maxiro-samurai/M-heat/Image/1.bmp

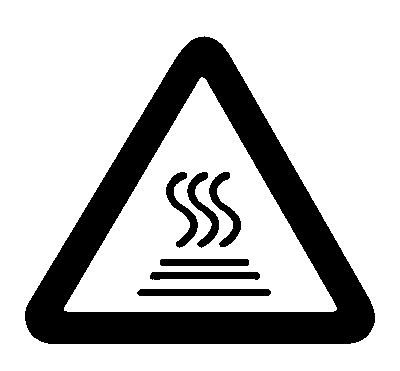
Image/1.bmp
