maxiro-samurai/M-heat/Image/e9a1dba946c36db57aece537687ce84.jpg

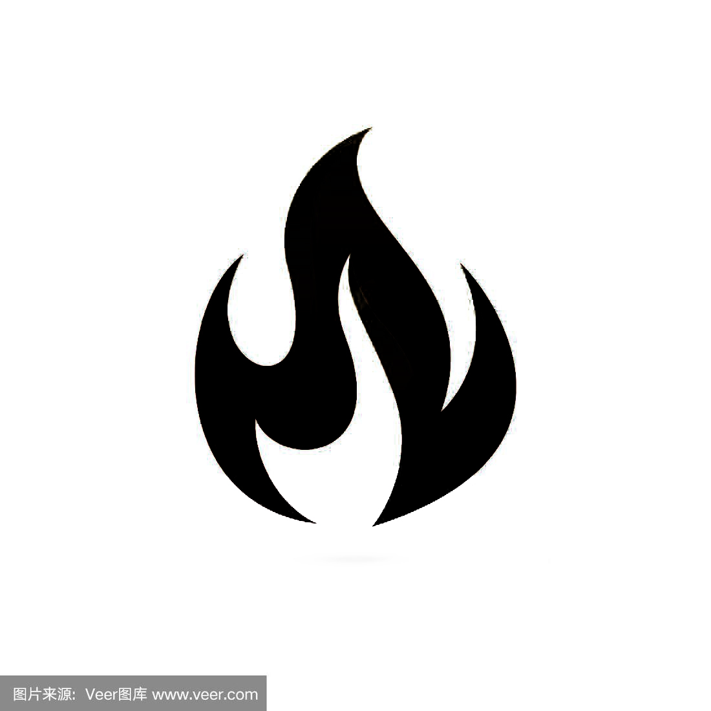
Image/e9a1dba946c36db57aece537687ce84.jpg
