maxiro-samurai/M-heat/Image/fire.bmp

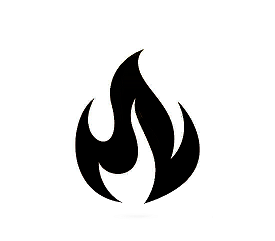
Image/fire.bmp
