maxiro-samurai/M-heat/Image/IMG_1925.JPG

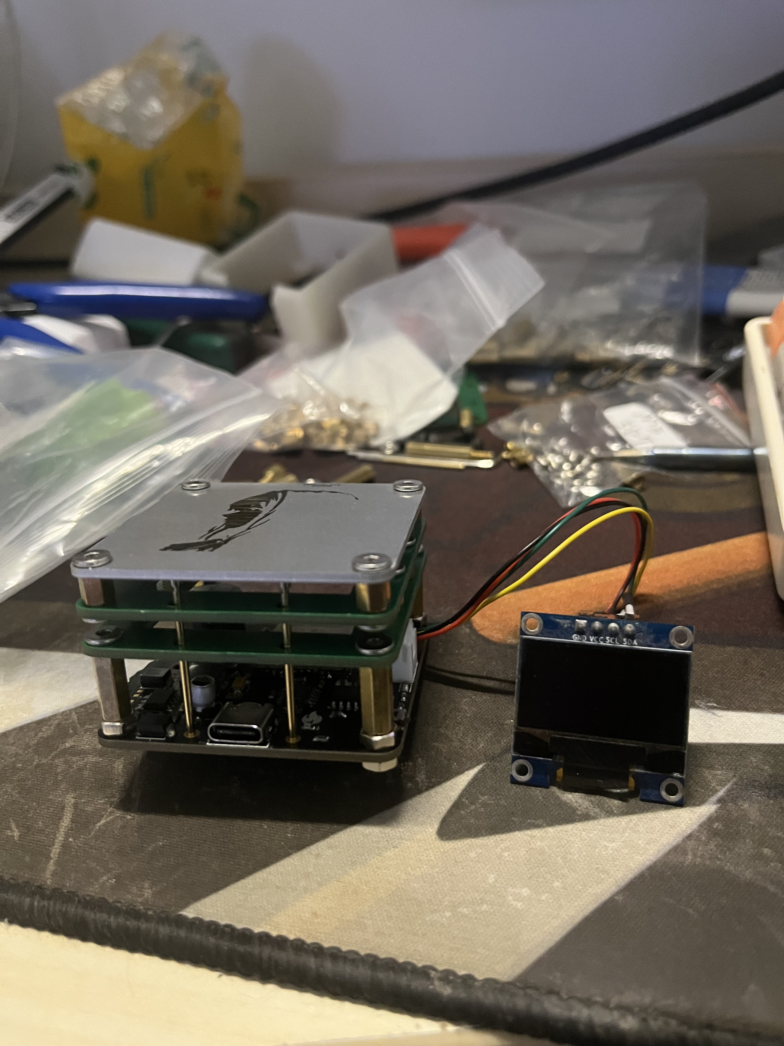
Image/IMG_1925.JPG
