maxiro-samurai/M-heat/Image/IMG_1926.JPG

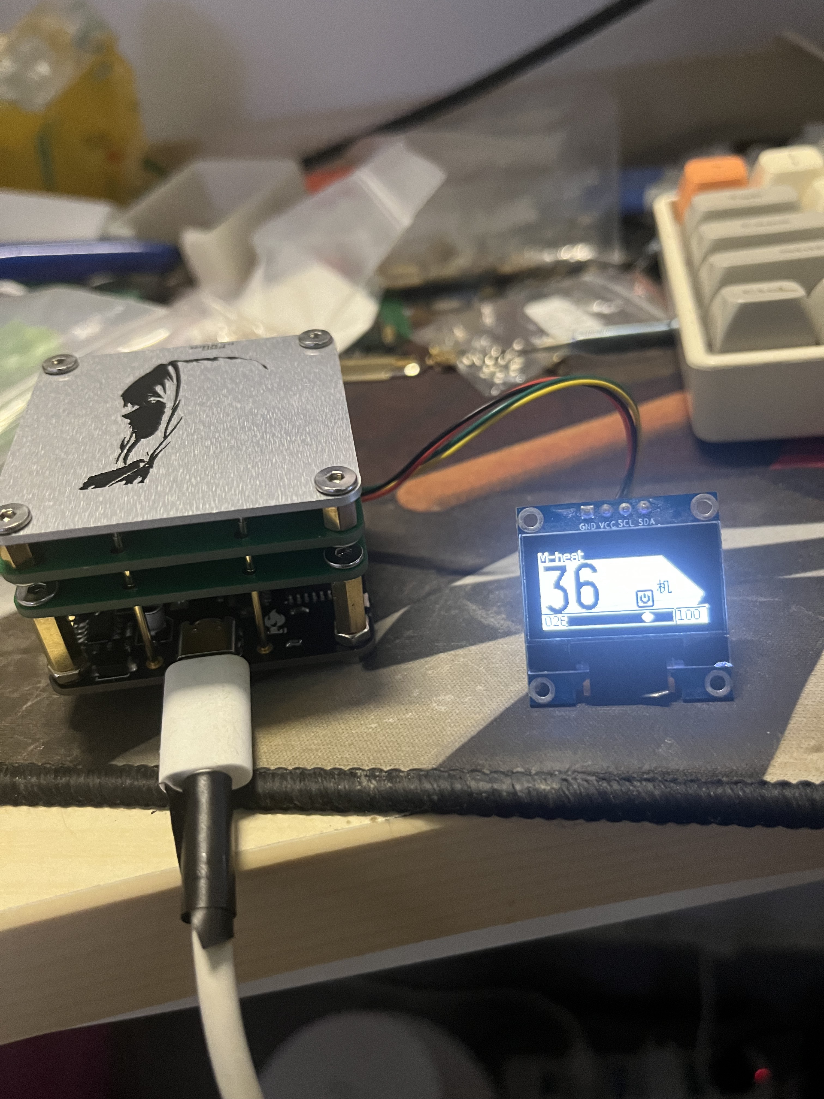
Image/IMG_1926.JPG
