maxiro-samurai/M-heat/Image/IMG_1927.JPG

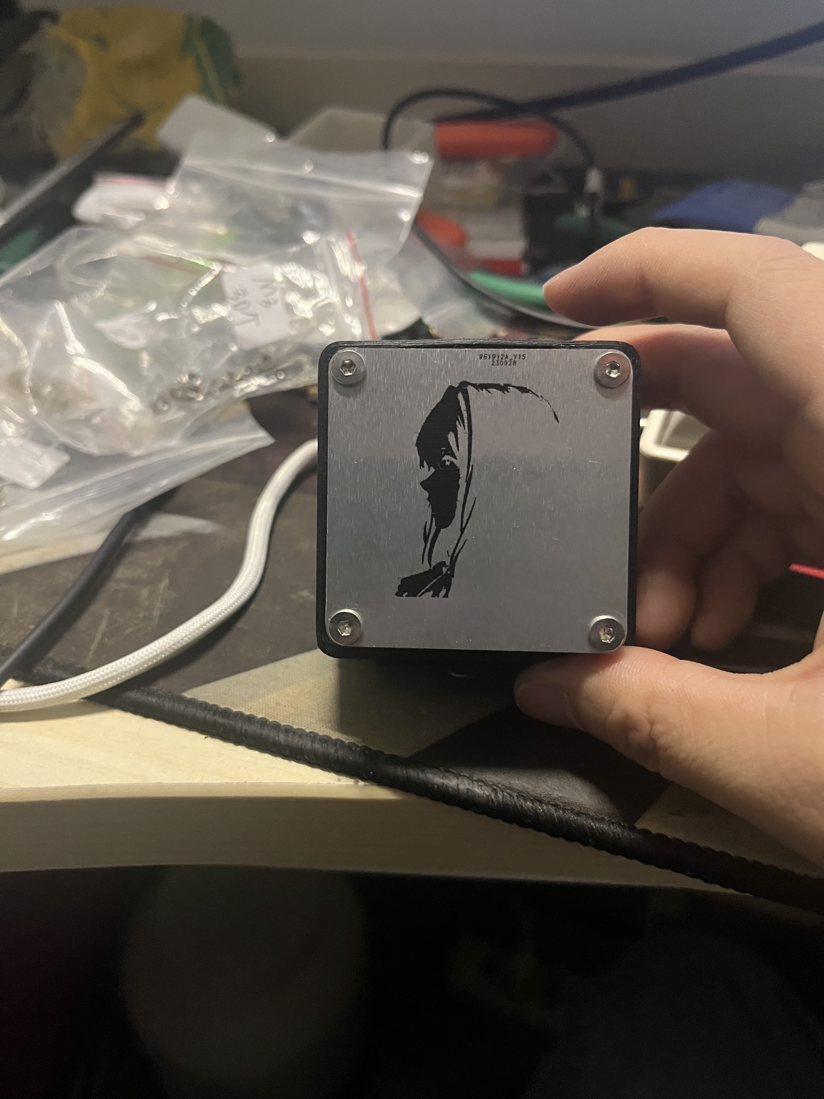
Image/IMG_1927.JPG
