maxiro-samurai/M-heat/Image/IMG_1928.JPG

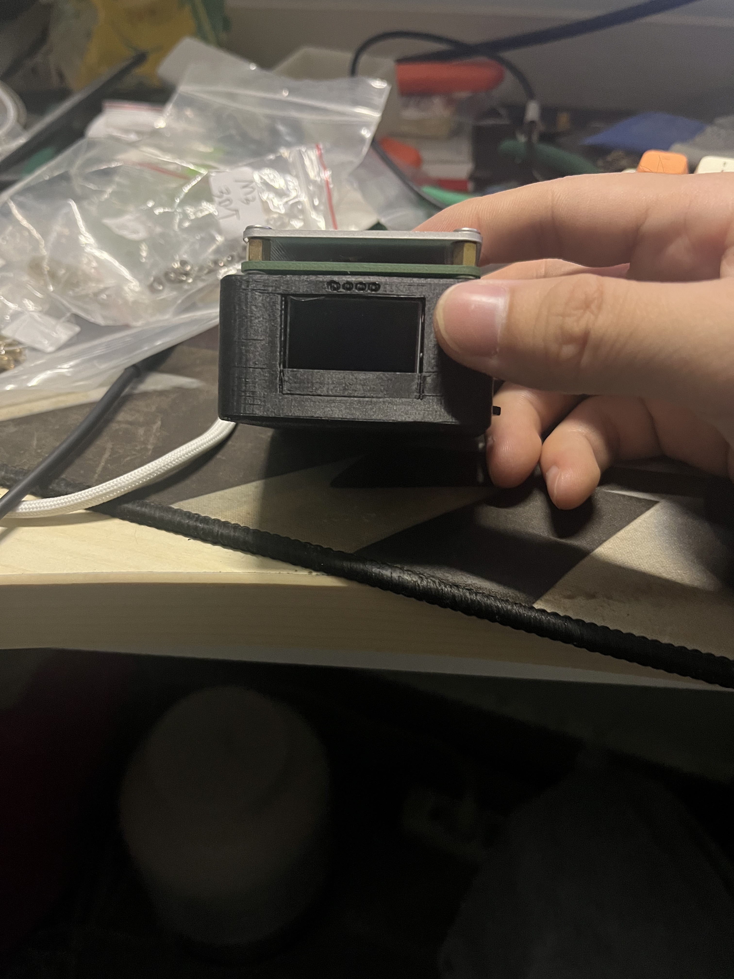
Image/IMG_1928.JPG
