maxiro-samurai/M-heat/Image/IMG_1987.JPG

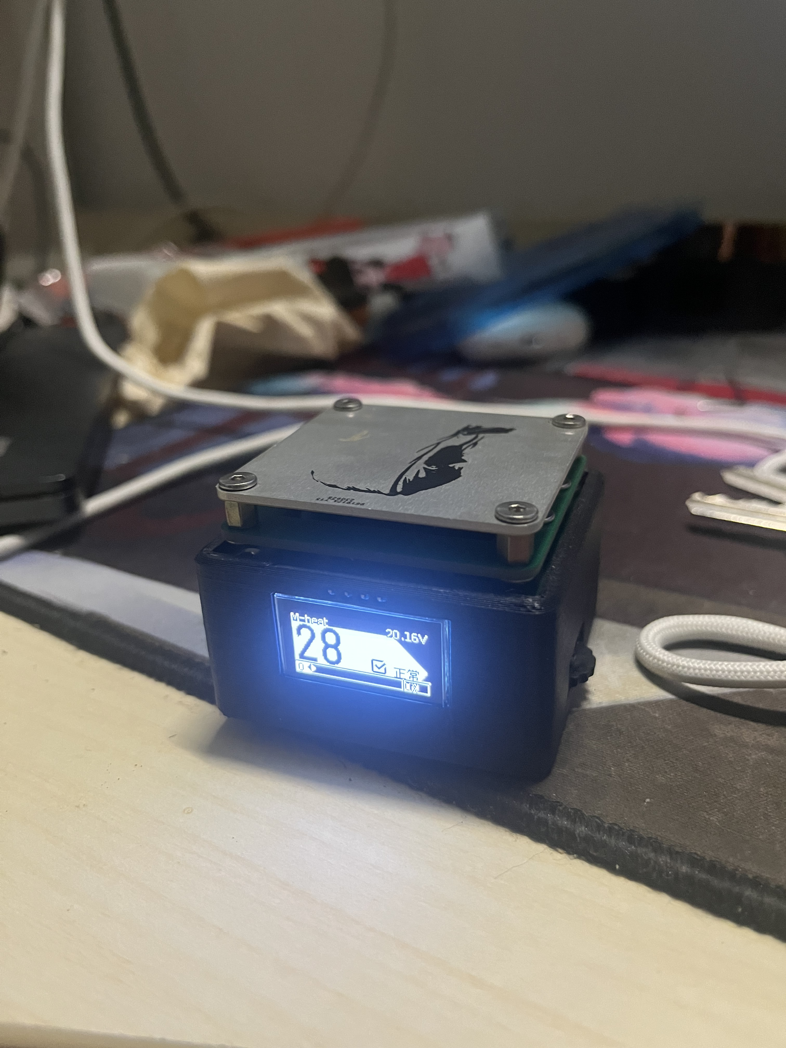
Image/IMG_1987.JPG
