maxiro-samurai/M-heat/Image/IMG_1988.JPG

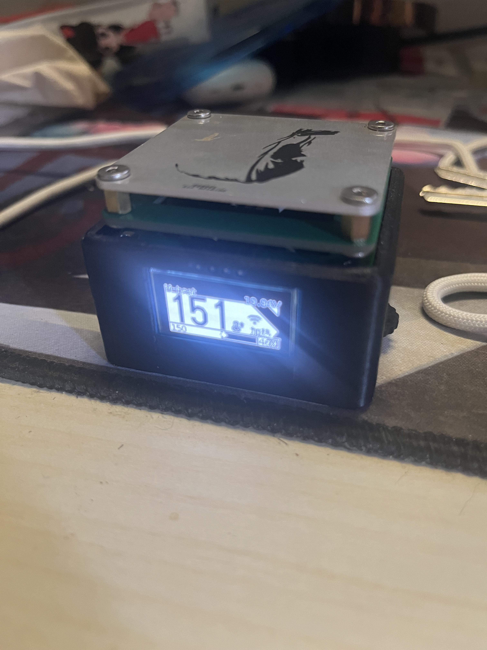
Image/IMG_1988.JPG
