maxiro-samurai/M-heat/Image/voilet.bmp

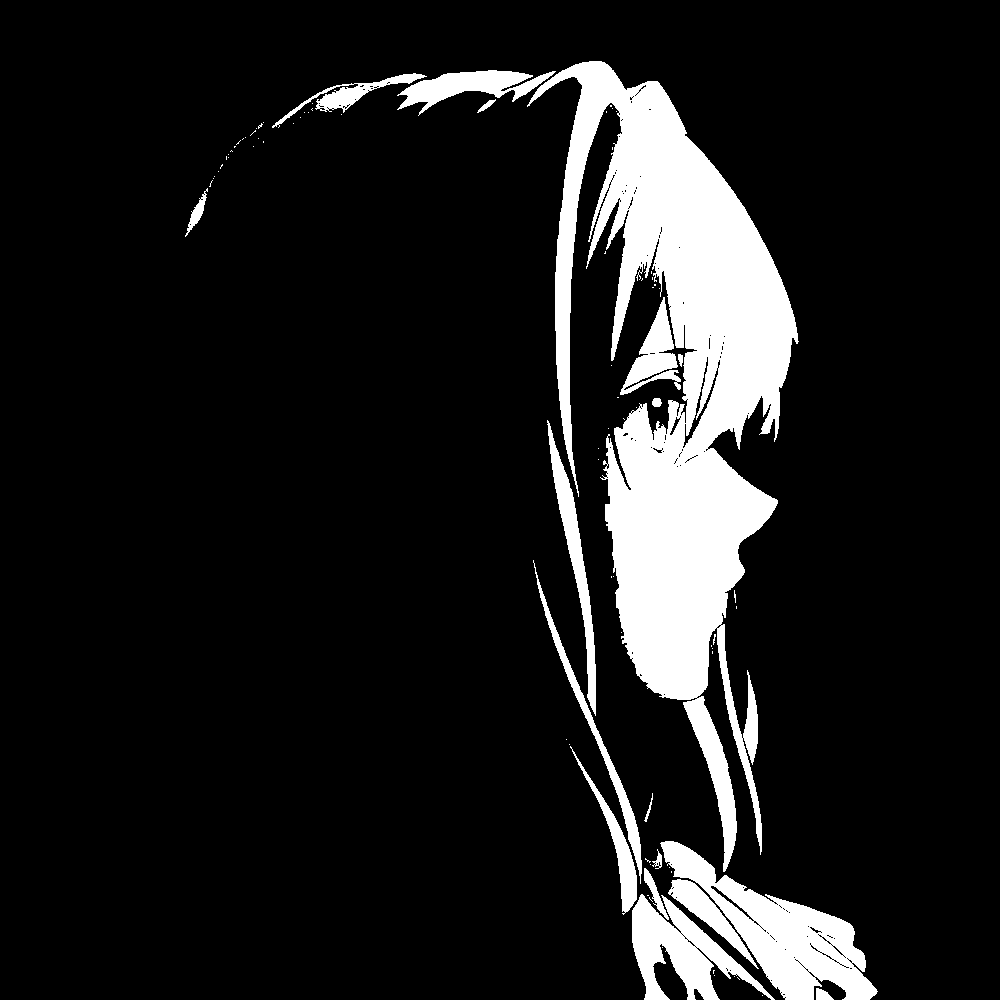
Image/voilet.bmp
