maxiro-samurai/M-heat/Image/wifi_0_01.bmp

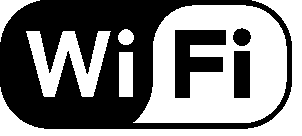
Image/wifi_0_01.bmp
