maxiro-samurai/M-heat/Image/xidian.bmp

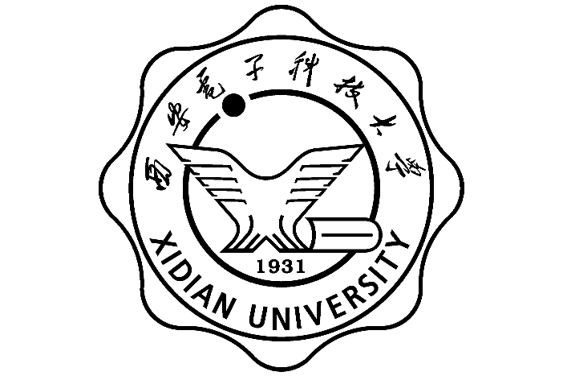
Image/xidian.bmp
