maxiro-samurai/M-heat/Image/高溫危險.bmp

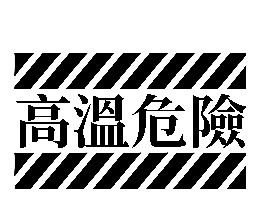
Image/高溫危險.bmp
