maxiro-samurai/M-heat/Software/esp32/components/adc/adc.c

#include "adc.h"

float system_vol ;
// static adc_channel_t channel[2] = {ADC_CHANNEL_6, ADC_CHANNEL_7};
// static adc_continuous_handle_t handle = NULL;
// static TaskHandle_t s_task_handle;
static const char *TAG = "EXAMPLE";
adc_continuous_item ADC = {
    .adc_buffer_1 = {0},
    .adc_buffer_2 = {0},
    .vol_low = 0,
    .vol_high = 0,
    .adc_error = 0,
    .now_temp = 0,
    .now_temp_high = 0,
    .set_temp = 0,
    .adc_get_temp_flg = false,
    .hotbed_max_temp = 255,
    .adc_max_temp = 255,
    .adc_max_temp_auto_flg = true,
};


static bool example_adc_calibration_init(adc_unit_t unit, adc_channel_t channel, adc_atten_t atten, adc_cali_handle_t *out_handle);
static void example_adc_calibration_deinit(adc_cali_handle_t handle);
// static bool IRAM_ATTR s_conv_done_cb(adc_continuous_handle_t handle, const adc_continuous_evt_data_t *edata, void *user_data)
// {
//     BaseType_t mustYield = pdFALSE;
//     //Notify that ADC continuous driver has done enough number of conversions
//     vTaskNotifyGiveFromISR(s_task_handle, &mustYield);

//     return (mustYield == pdTRUE);
// }

// static void continuous_adc_init(adc_channel_t *channel, uint8_t channel_num, adc_continuous_handle_t *out_handle)
// {
//     adc_continuous_handle_t handle = NULL;     // 持续读取ADC事件句柄

//     adc_continuous_handle_cfg_t adc_config = {  //缓冲区配置
//         .max_store_buf_size = 1024,
//         .conv_frame_size = EXAMPLE_READ_LEN,
//     };
//     ESP_ERROR_CHECK(adc_continuous_new_handle(&adc_config, &handle));

//     adc_continuous_config_t dig_cfg = {
//         .sample_freq_hz = 20 * 1000,
//         .conv_mode = EXAMPLE_ADC_CONV_MODE,    //单通道转换模式
//         .format = EXAMPLE_ADC_OUTPUT_TYPE,     //DMA输出格式
//     };

//     adc_digi_pattern_config_t adc_pattern[SOC_ADC_PATT_LEN_MAX] = {0};
//     dig_cfg.pattern_num = channel_num;
//     for (int i = 0; i < channel_num; i++) {
//         adc_pattern[i].atten = EXAMPLE_ADC_ATTEN;
//         adc_pattern[i].channel = channel[i] & 0x7;
//         adc_pattern[i].unit = EXAMPLE_ADC_UNIT;
//         adc_pattern[i].bit_width = EXAMPLE_ADC_BIT_WIDTH;

//         ESP_LOGI(TAG, "adc_pattern[%d].atten is :%"PRIx8, i, adc_pattern[i].atten);
//         ESP_LOGI(TAG, "adc_pattern[%d].channel is :%"PRIx8, i, adc_pattern[i].channel);
//         ESP_LOGI(TAG, "adc_pattern[%d].unit is :%"PRIx8, i, adc_pattern[i].unit);
//     }
//     dig_cfg.adc_pattern = adc_pattern;
//     ESP_ERROR_CHECK(adc_continuous_config(handle, &dig_cfg));

//     *out_handle = handle;
// }



/*

获取电压值

*/
static void adc_oneshot_get_voltage(adc_oneshot_unit_handle_t adc1_handle,adc_cali_handle_t adc1_cali_chan0_handle ,adc_cali_handle_t adc1_cali_chan1_handle){
    uint8_t i;
    uint32_t adc_temp1 = 0;
    uint32_t adc_temp2 = 0;
    for (i = 0; i < 8; i++) //读8次ADC值 求平均
    {
        
        
        adc_oneshot_read(adc1_handle, ADC_CHANNEL_6, &ADC.adc_buffer_1[i]); //存储ADC值
        // ESP_LOGI(TAG, "ADC%d Channel[%d] Raw Data: %d", ADC_UNIT_1 + 1, EXAMPLE_ADC1_CHAN0, ADC.adc_buffer_1[i]);
        adc_oneshot_read(adc1_handle, ADC_CHANNEL_7, &ADC.adc_buffer_2[i]); //存储ADC值
        // ESP_LOGI(TAG, "ADC%d Channel[%d] Raw Data: %d", ADC_UNIT_1 + 1, EXAMPLE_ADC1_CHAN1, adc_raw[0][1]);
        adc_temp1 += ADC.adc_buffer_1[i]; //低电平ADC值
        adc_temp2 += ADC.adc_buffer_2[i]; //高电平ADC值
    }
    
    adc_temp1 >>= 3; //平均值滤波
    adc_temp2 >>= 3; //
    
    
    ESP_ERROR_CHECK(adc_cali_raw_to_voltage(adc1_cali_chan0_handle, adc_temp1, &ADC.vol_low));
    ESP_LOGI(TAG, "ADC%d Channel[%d] Cali Voltage: %lu mV", ADC_UNIT_1 + 1, ADC_CHANNEL_6, ADC.vol_low);


    ESP_ERROR_CHECK(adc_cali_raw_to_voltage(adc1_cali_chan1_handle, adc_temp2, &ADC.vol_high));
    ESP_LOGI(TAG, "ADC%d Channel[%d] Cali Voltage: %lu mV", ADC_UNIT_1 + 1, ADC_CHANNEL_7, ADC.vol_high);

    
    
}

static void adc_get_sys_vol(adc_oneshot_unit_handle_t adc1_handle,adc_cali_handle_t adc1_cali_chan0_handle )
{
    uint32_t adc_temp;
    uint32_t vol_temp;
    adc_oneshot_read(adc1_handle, ADC_CHANNEL_5, &adc_temp); //存储ADC值

    ESP_ERROR_CHECK(adc_cali_raw_to_voltage(adc1_cali_chan0_handle, adc_temp, &vol_temp));
    // printf("%lu",vol_temp);
    system_vol = (float)(vol_temp*20.0f/1000.0f);
    
}
// static void adc_get_value(adc_continuous_item *adc) {

//     uint32_t ret_num = 0;
//     uint8_t result[EXAMPLE_READ_LEN] = {0};
//     esp_err_t ret;
//     uint8_t m = 0;
//     uint8_t n = 0;
//     memset(result, 0xcc, EXAMPLE_READ_LEN);

//     ulTaskNotifyTake(pdTRUE, portMAX_DELAY); //等待通知

//     while (1) {
//         ret = adc_continuous_read(handle, result, EXAMPLE_READ_LEN, &ret_num, 0);
//         if (ret == ESP_OK) {
//             ESP_LOGI("TASK", "ret is %x, ret_num is %"PRIu32" bytes", ret, ret_num);
//             for (int i = 0; i < ret_num; i += SOC_ADC_DIGI_RESULT_BYTES) {
//                 adc_digi_output_data_t *p = (void*)&result[i];
//                 uint32_t chan_num = EXAMPLE_ADC_GET_CHANNEL(p);
//                 uint32_t data = EXAMPLE_ADC_GET_DATA(p);
                
//                 if (chan_num == ADC_CHANNEL_6 ){
//                     // ESP_LOGI(TAG, "ADC_CHANNEL_6 data is :%lu", data);
//                     adc->adc_buffer_1[m] = data; //存储ADC值
                    
//                     m++;
//                     if (m >= 8) {
//                         m = 0;
//                     }
//                 } else if (chan_num == ADC_CHANNEL_7 )
//                 {
//                     // ESP_LOGI(TAG, "ADC_CHANNEL_7 data is :%lu", data);
//                     adc->adc_buffer_2[n] = data; //存储ADC值
//                     n++;
//                     if (n >= 8) {
//                         n = 0;
//                     }
//                 }
//             }
//             //  vTaskDelay(1);
//             } else if (ret == ESP_ERR_TIMEOUT) {
            
//                 break;
//             }
//         }

//     }


// static void adc_voltage(adc_continuous_item *adc)
// {
//     uint8_t i;
//     for (i = 0; i < 8; i++)
//     {
//         adc->vol_low += adc->adc_buffer_1[i]; //低电平ADC值
//         adc->vol_high += adc->adc_buffer_2[i]; //高电平ADC值
//     }
//     adc->vol_low >>= 3; //平均值滤波
//     adc->vol_high >>= 3; //

//     adc->vol_low = adc->vol_low * 1000 / 4095; //转换为电压值
//     adc->vol_high = adc->vol_high * 1000 / 4095; //转换为电压值
//     ESP_LOGI(TAG, "vol_low is :%lu", adc->vol_low);
//     ESP_LOGI(TAG, "vol_high is :%lu", adc->vol_high);
// }







static void adc_temp(adc_continuous_item *adc){

    int32_t rt;
    int32_t tt;
    int32_t temp_buf = 0;
    double buf;
    
    //低温情况下直接返回温度
    rt = adc->vol_low * 1000 / ((3300 - adc->vol_low) / 13);
    adc->now_temp = (100 / (log(rt / 10000.0) / 3950 + 1 / 298.15) - 27315) / 100; //转换为温度值
    // ESP_LOGI(TAG, "now_temp is :%u", adc->now_temp);
    if (adc->now_temp < 100)
        return;
    // //

    // //首次加热到高温时，记录当前温度
    if (adc->now_temp < 105 && !adc->adc_error)
    {
        // if (pwm.power || adc_max_temp_auto_flg == 0)
        if (PWM_state || adc->adc_max_temp_auto_flg == 0)
            temp_buf = adc->now_temp;
    }

    adc->vol_high = adc->vol_high / 21;

    buf = adc->vol_high * 1000 / ((3300 - adc->vol_high) / 13.0);
    tt = (100 / (log(buf / 10000) / 3950 + 1 / 298.15) - 27315) / 100;
    ESP_LOGI(TAG, "tt is :%ld", tt);
    adc->now_temp_high = tt;
    
    // 当前温度减去放大器放大后的温度值，即为ADC误差值
    if (temp_buf)
        adc->adc_error = temp_buf - tt;

    if (adc->adc_max_temp_auto_flg)
    {
        //高于150度时，进行温度补偿
        int16_t tmp = 100 - adc->adc_error;
        //热床最大值减去ADC误差值
        rt = adc->hotbed_max_temp - adc->adc_error;
        //ADC最大值与热床最大值差值
        int16_t tmp1 = adc->adc_max_temp - rt;
        //总误差/高温阶段的量程，高温阶段单位量程内产生的误差
        buf = (double)(tmp1) / (double)(adc->adc_max_temp - tmp);
        // 高温矫正
        tt = (double)tt - ((double)(tt - tmp) * buf);
    }
    // 最终温度矫正
    adc->now_temp = (adc->adc_max_temp_auto_flg) ? (tt + adc->adc_error) : tt;
}

// void adc_continuous_read_task(void *arg)
// {
    
//     // memset(result, 0xcc, EXAMPLE_READ_LEN);

//     s_task_handle = xTaskGetCurrentTaskHandle(); //获取任务句柄

//     continuous_adc_init(channel, sizeof(channel) / sizeof(adc_channel_t), &handle); //初始化ADC

//     adc_continuous_evt_cbs_t cbs = {
//         .on_conv_done = s_conv_done_cb,
//     };   

//     ESP_ERROR_CHECK(adc_continuous_register_event_callbacks(handle, &cbs, NULL));//注册中断回调函数
//     ESP_ERROR_CHECK(adc_continuous_start(handle));  //启动ADC

//     while (1)
//     {


//         // adc_get_value(&ADC); //获取ADC值
//         // adc_voltage(&ADC); //获取电压值
//         // // calculate_temperature(&ADC); //计算温度值
//         // adc_temp(&ADC); //获取温度值
//         // // adc_voltage(&ADC);
//         // vTaskDelay(1000); //延时1ms
        
//     }
    
// }

void adc_oneshot_read_task(void *arg)
{
    //-------------ADC1 Init---------------//
    adc_oneshot_unit_handle_t adc1_handle;
    adc_oneshot_unit_init_cfg_t init_config1 = {
        .unit_id = ADC_UNIT_1,
    };
    ESP_ERROR_CHECK(adc_oneshot_new_unit(&init_config1, &adc1_handle));

    //-------------ADC1 Config---------------//
    adc_oneshot_chan_cfg_t config = {
        .bitwidth = ADC_BITWIDTH_DEFAULT,
        .atten = ADC_ATTEN_DB_0,
    };
    // 系统电压检测
    ESP_ERROR_CHECK(adc_oneshot_config_channel(adc1_handle, ADC_CHANNEL_5, &config));
    config.atten = EXAMPLE_ADC_ATTEN;
    // 热敏电阻
    ESP_ERROR_CHECK(adc_oneshot_config_channel(adc1_handle, ADC_CHANNEL_6, &config));
    ESP_ERROR_CHECK(adc_oneshot_config_channel(adc1_handle, ADC_CHANNEL_7, &config));

    //-------------ADC1 Calibration Init---------------//
    adc_cali_handle_t adc1_cali_chan0_handle = NULL;
    adc_cali_handle_t adc1_cali_chan1_handle = NULL;
    adc_cali_handle_t adc1_cali_chan2_handle = NULL;
    
    bool do_calibration1_chan0 = example_adc_calibration_init(ADC_UNIT_1, ADC_CHANNEL_6, EXAMPLE_ADC_ATTEN, &adc1_cali_chan0_handle);
    bool do_calibration1_chan1 = example_adc_calibration_init(ADC_UNIT_1, ADC_CHANNEL_7, EXAMPLE_ADC_ATTEN, &adc1_cali_chan1_handle);
    bool do_calibration1_chan2 = example_adc_calibration_init(ADC_UNIT_1, ADC_CHANNEL_5, ADC_ATTEN_DB_0, &adc1_cali_chan2_handle);



    while (1)
    {
        adc_oneshot_get_voltage(adc1_handle,adc1_cali_chan0_handle,adc1_cali_chan1_handle); //获取电压值
        adc_get_sys_vol(adc1_handle,adc1_cali_chan2_handle);
        adc_temp(&ADC); //获取温度值
        vTaskDelay(100); //延时1ms
    }



}


/*---------------------------------------------------------------
        ADC Calibration
---------------------------------------------------------------*/
static bool example_adc_calibration_init(adc_unit_t unit, adc_channel_t channel, adc_atten_t atten, adc_cali_handle_t *out_handle)
{
    adc_cali_handle_t handle = NULL;
    esp_err_t ret = ESP_FAIL;
    bool calibrated = false;

if (!calibrated) {
        ESP_LOGI(TAG, "calibration scheme version is %s", "Line Fitting");
        adc_cali_line_fitting_config_t cali_config = {
            .unit_id = unit,
            .atten = atten,
            .bitwidth = ADC_BITWIDTH_DEFAULT,
        };
        ret = adc_cali_create_scheme_line_fitting(&cali_config, &handle);
        if (ret == ESP_OK) {
            calibrated = true;
        }
}


    *out_handle = handle;
    if (ret == ESP_OK) {
        ESP_LOGI(TAG, "Calibration Success");
    } else if (ret == ESP_ERR_NOT_SUPPORTED || !calibrated) {
        ESP_LOGW(TAG, "eFuse not burnt, skip software calibration");
    } else {
        ESP_LOGE(TAG, "Invalid arg or no memory");
    }

    return calibrated;
}

static void example_adc_calibration_deinit(adc_cali_handle_t handle)
{
    ESP_LOGI(TAG, "deregister %s calibration scheme", "Line Fitting");
    ESP_ERROR_CHECK(adc_cali_delete_scheme_line_fitting(handle));

}
