maxiro-samurai/M-heat/Software/esp32/components/externdraw/bitmap.c

//128x64
#include "bitmap.h"



uint8_t Logo[] = {0x00, 0x00, 0x00, 0x00, 0x00, 0x00, 0x00, 0x00, 0x00, 0x00, 0x00, 0x00, 0x00, 0x00, 0x00,
    0x00, 0x00, 0x00, 0x00, 0x00, 0x00, 0x00, 0x00, 0x00, 0x00, 0x00, 0x00, 0x00, 0x00, 0x00,
    0x00, 0x00, 0x00, 0x00, 0x00, 0x00, 0x00, 0x00, 0x00, 0x00, 0x00, 0x02, 0xf7, 0x7a, 0x00,
    0x00, 0x00, 0x00, 0x00, 0x00, 0x00, 0x00, 0x00, 0x00, 0x00, 0x00, 0x00, 0x00, 0x12, 0x40,
    0x00, 0x00, 0x00, 0x00, 0x00, 0x00, 0x00, 0x00, 0x00, 0x00, 0x00, 0x00, 0x00, 0x00, 0x3f,
    0xe0, 0x00, 0x00, 0x00, 0x00, 0x00, 0x00, 0x03, 0xff, 0xfc, 0x00, 0x7f, 0xff, 0x81, 0xfe,
    0x12, 0x43, 0xff, 0x00, 0x00, 0x00, 0x00, 0x00, 0x00, 0x00, 0x00, 0x38, 0x00, 0x00, 0x00,
    0x00, 0x1d, 0xc0, 0x00, 0x00, 0x00, 0x00, 0x00, 0x00, 0x03, 0xff, 0xfc, 0x7c, 0x7f, 0xff,
    0x01, 0xfe, 0x0f, 0x83, 0xff, 0xf8, 0x00, 0x00, 0x00, 0x00, 0x03, 0xff, 0xfc, 0x7c, 0x7f,
    0xff, 0x01, 0xff, 0x00, 0x07, 0xff, 0xf8, 0x00, 0x00, 0x00, 0x00, 0x00, 0x3e, 0x70, 0x7c,
    0x19, 0xf0, 0x01, 0xff, 0x0f, 0x87, 0xff, 0x00, 0x00, 0x00, 0x00, 0x00, 0x00, 0x0e, 0xf0,
    0x7c, 0x1d, 0xc0, 0x01, 0xff, 0x1f, 0xc7, 0xff, 0x00, 0x00, 0x00, 0x00, 0x00, 0x00, 0x07,
    0xe0, 0x7c, 0x0f, 0x80, 0x00, 0x3f, 0x1f, 0xc7, 0xe0, 0x00, 0x00, 0x00, 0x00, 0x00, 0x00,
    0x07, 0xe0, 0x7c, 0x0f, 0x80, 0x00, 0x1f, 0x1b, 0x47, 0xc0, 0x00, 0x00, 0x00, 0x00, 0x00,
    0x00, 0x07, 0xe0, 0x7c, 0x0f, 0x80, 0x00, 0x1f, 0x1b, 0x47, 0xc0, 0x00, 0x00, 0x00, 0x00,
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
    0x6d, 0x80, 0xde, 0xc0, 0xbf, 0x40, 0xbf, 0x40, 0xde, 0xc0, 0x61, 0x80, 0x3f, 0x00};
uint8_t c7[]  = {0x1f, 0xe0, 0x3f, 0xf0, 0x70, 0x38, 0x60, 0x18, 0x60, 0x18, 0x60, 0x18, 0xff, 0xfc,
    0xfc, 0xfc, 0xfc, 0xfc, 0xfc, 0xfc, 0xf8, 0x7c, 0xf8, 0x7c, 0xfc, 0xfc, 0x7f, 0xf8};
