maxiro-samurai/M-heat/Software/esp32/components/externdraw/bitmap.h

#ifndef BITMAP_H
#define BITMAP_H


#include <stdint.h>
//128x64
extern uint8_t Logo[];



extern uint8_t PositioningCursor[];
extern uint8_t Battery_NoPower[];
extern uint8_t Lightning[];
//状态提示图标
//width:14,height:14
extern uint8_t c1[];
extern uint8_t c2[];
extern uint8_t c3[];
extern uint8_t c5[];
extern uint8_t c6[];
extern uint8_t c7[];
extern uint8_t* C_table[];
extern uint8_t epd_bitmap_wifi_solid[];
extern uint8_t IMG_BLE_S[];

#endif
